scottericpetersen/CAFFEINE/paper/logs/group_test/endpoint_log_pod3_grp.csv

system_time | remote_timestamp | latency_ms | sequence_number
2025-05-15T11:13:07.513176 | 1747321987.007723 | 505.432 | 0
2025-05-15T11:13:07.515925 | 1747321987.017425 | 498.486 | 1
2025-05-15T11:13:07.518675 | 1747321987.027419 | 491.247 | 2
2025-05-15T11:13:07.521302 | 1747321987.397427 | 123.865 | 39
2025-05-15T11:13:07.523168 | 1747321987.407426 | 115.732 | 40
2025-05-15T11:13:07.523786 | 1747321987.417427 | 106.354 | 41
2025-05-15T11:13:07.525354 | 1747321987.427426 | 97.92 | 42
2025-05-15T11:13:07.526999 | 1747321987.437427 | 89.564 | 43
2025-05-15T11:13:07.528279 | 1747321987.457427 | 70.845 | 45
2025-05-15T11:13:07.528917 | 1747321987.447426 | 81.481 | 44
2025-05-15T11:13:07.532104 | 1747321987.467426 | 64.671 | 46
2025-05-15T11:13:07.532553 | 1747321987.477427 | 55.121 | 47
2025-05-15T11:13:07.534322 | 1747321987.487427 | 46.89 | 48
2025-05-15T11:13:07.536326 | 1747321987.497427 | 38.891 | 49
2025-05-15T11:13:07.536886 | 1747321987.507427 | 29.455 | 50
2025-05-15T11:13:07.537390 | 1747321987.517427 | 19.956 | 51
2025-05-15T11:13:07.544280 | 1747321987.527427 | 16.845 | 52
2025-05-15T11:13:07.554681 | 1747321987.537427 | 17.248 | 53
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
