scottericpetersen/CAFFEINE/paper/logs/single_tests/endpoint_log_pod1.csv

system_time | remote_timestamp | latency_ms | sequence_number
2025-05-15T10:38:45.889145 | 1747319924.829069 | 1060.061 | 0
2025-05-15T10:38:45.890400 | 1747319925.834085 | 56.305 | 1
2025-05-15T10:38:45.891751 | 1747319925.843692 | 48.051 | 2
2025-05-15T10:38:45.970882 | 1747319925.863703 | 107.163 | 4
2025-05-15T10:38:45.971901 | 1747319925.873694 | 98.206 | 5
2025-05-15T10:38:45.975954 | 1747319925.913693 | 62.253 | 9
2025-05-15T10:38:45.971991 | 1747319925.883692 | 88.297 | 6
2025-05-15T10:38:45.971718 | 1747319925.893693 | 77.856 | 7
2025-05-15T10:38:45.974419 | 1747319925.903691 | 70.715 | 8
2025-05-15T10:38:45.979967 | 1747319925.933692 | 46.263 | 11
2025-05-15T10:38:45.980275 | 1747319925.923693 | 56.58 | 10
2025-05-15T10:38:46.019493 | 1747319925.943693 | 75.794 | 12
2025-05-15T10:38:46.019986 | 1747319925.953692 | 66.29 | 13
2025-05-15T10:38:46.090310 | 1747319925.963691 | 126.611 | 14
2025-05-15T10:38:46.093204 | 1747319925.973693 | 119.503 | 15
2025-05-15T10:38:46.094900 | 1747319925.983693 | 111.199 | 16
2025-05-15T10:38:46.097762 | 1747319925.993692 | 104.064 | 17
2025-05-15T10:38:46.098465 | 1747319926.003692 | 94.765 | 18
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
