scottericpetersen/CAFFEINE/paper/logs/single_tests/endpoint_log_pod2.csv

system_time | remote_timestamp | latency_ms | sequence_number
2025-05-15T10:51:22.721829 | 1747320682.204614 | 517.201 | 0
2025-05-15T10:51:22.724334 | 1747320682.214574 | 509.746 | 1
2025-05-15T10:51:22.732373 | 1747320682.614575 | 117.79 | 41
2025-05-15T10:51:22.733591 | 1747320682.224572 | 509.002 | 2
2025-05-15T10:51:22.734574 | 1747320682.604577 | 129.982 | 40
2025-05-15T10:51:22.734827 | 1747320682.624576 | 110.248 | 42
2025-05-15T10:51:22.736163 | 1747320682.634575 | 101.577 | 43
2025-05-15T10:51:22.742255 | 1747320682.654575 | 87.672 | 45
2025-05-15T10:51:22.742499 | 1747320682.664576 | 77.92 | 46
2025-05-15T10:51:22.743621 | 1747320682.644577 | 99.038 | 44
2025-05-15T10:51:22.745315 | 1747320682.674575 | 70.732 | 47
2025-05-15T10:51:22.748814 | 1747320682.684576 | 64.229 | 48
2025-05-15T10:51:22.749644 | 1747320682.694575 | 55.063 | 49
2025-05-15T10:51:22.750121 | 1747320682.704576 | 45.54 | 50
2025-05-15T10:51:22.750343 | 1747320682.714575 | 35.758 | 51
2025-05-15T10:51:22.751264 | 1747320682.724576 | 26.685 | 52
2025-05-15T10:51:22.752816 | 1747320682.734574 | 18.235 | 53
2025-05-15T10:51:22.762646 | 1747320682.744576 | 18.063 | 54
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
