scottericpetersen/CAFFEINE/paper/logs/single_tests/plots/all_pods_overlay.png

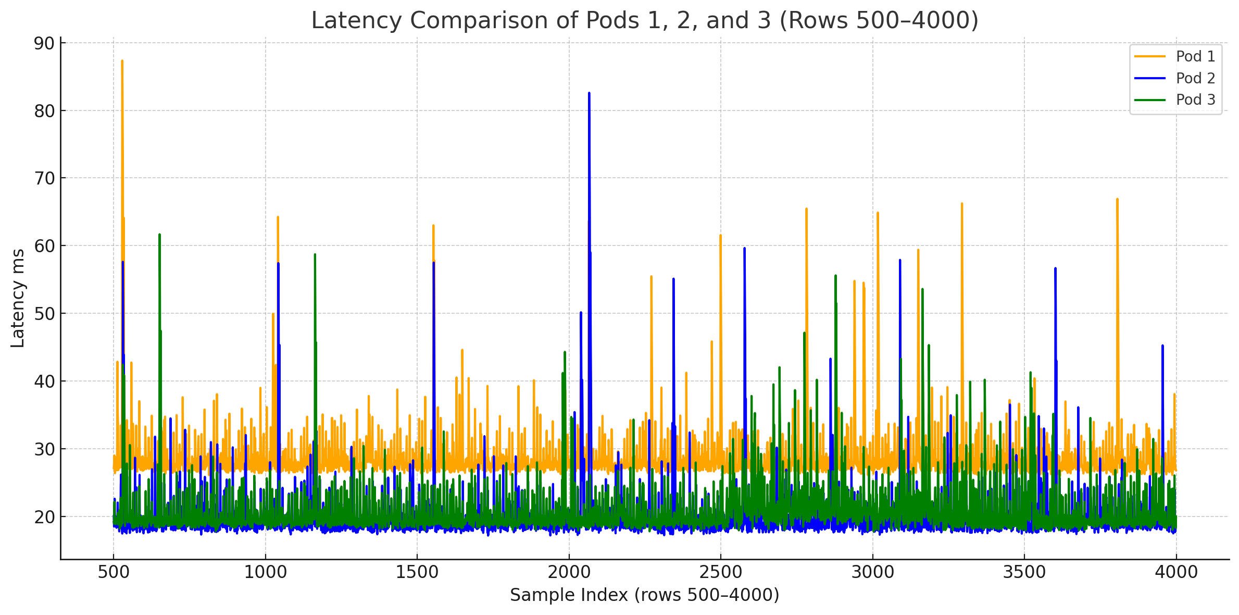
paper/logs/single_tests/plots/all_pods_overlay.png
