scottericpetersen/CAFFEINE/paper/logs/single_tests/plots/pod1_latency.png

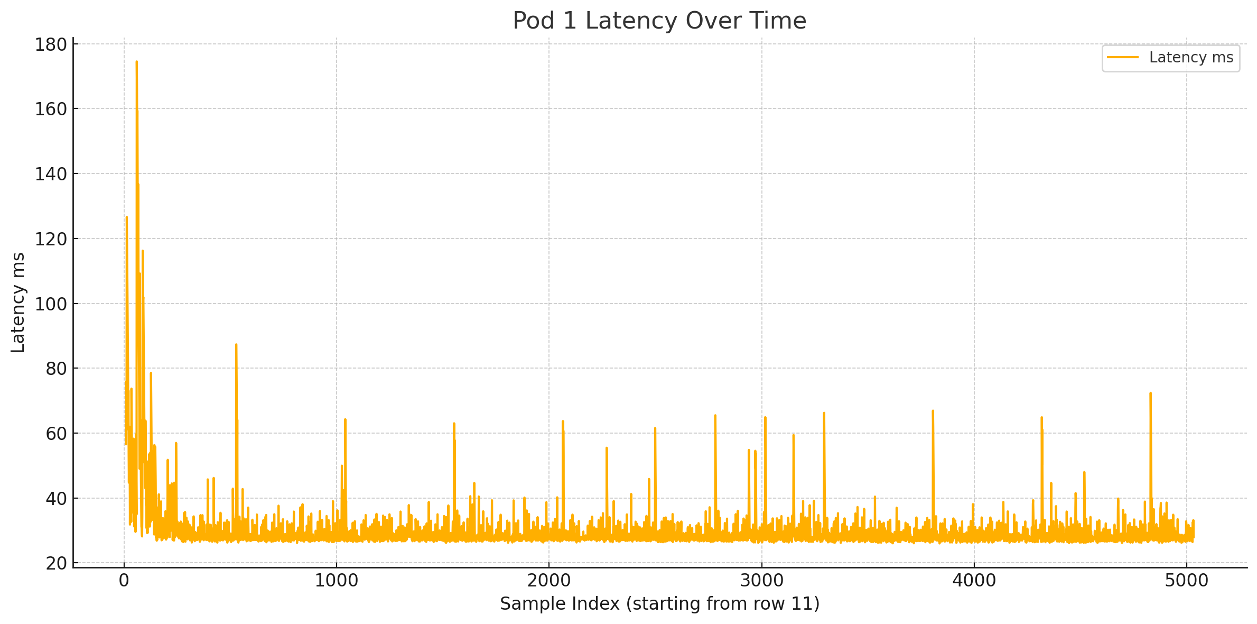
paper/logs/single_tests/plots/pod1_latency.png
