scottericpetersen/CAFFEINE/paper/logs/single_tests/plots/pod2_latency.png

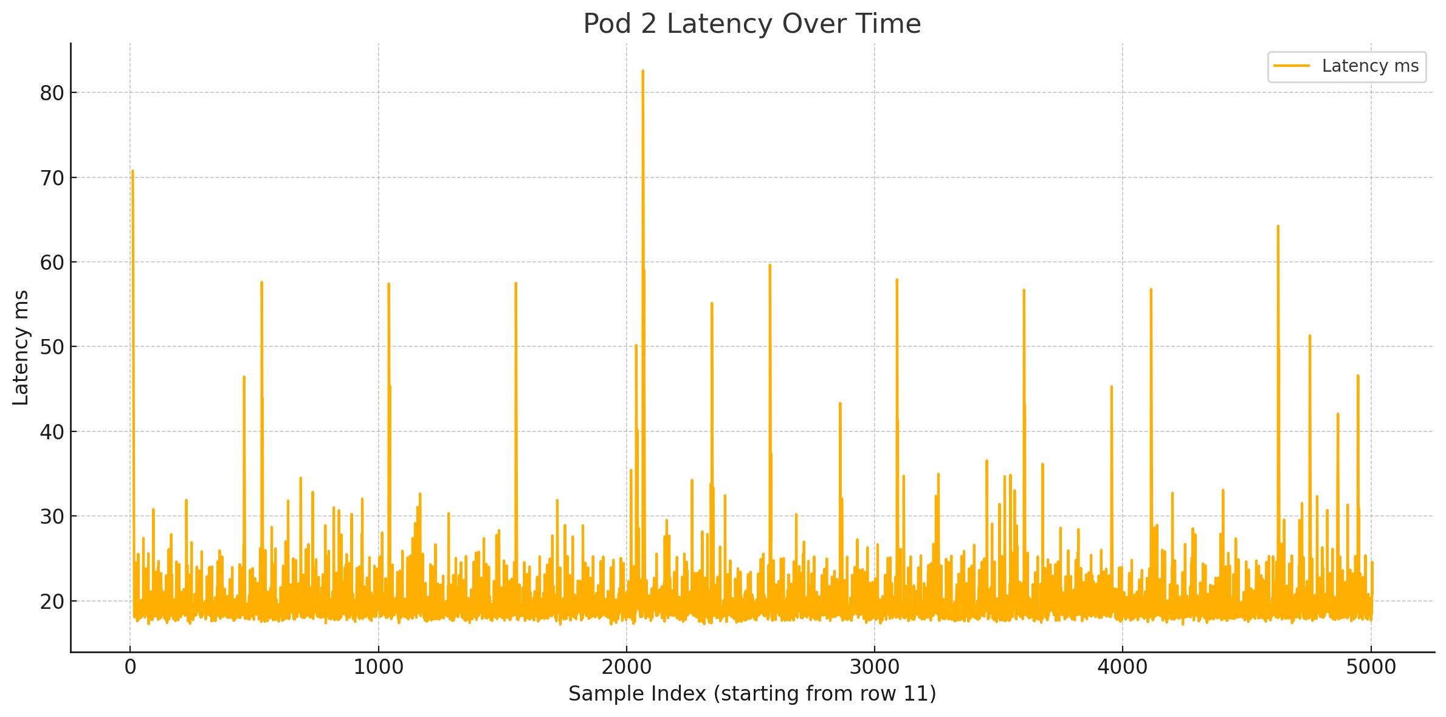
paper/logs/single_tests/plots/pod2_latency.png
