scottericpetersen/CAFFEINE/paper/logs/single_tests/plots/pod3_latency.png

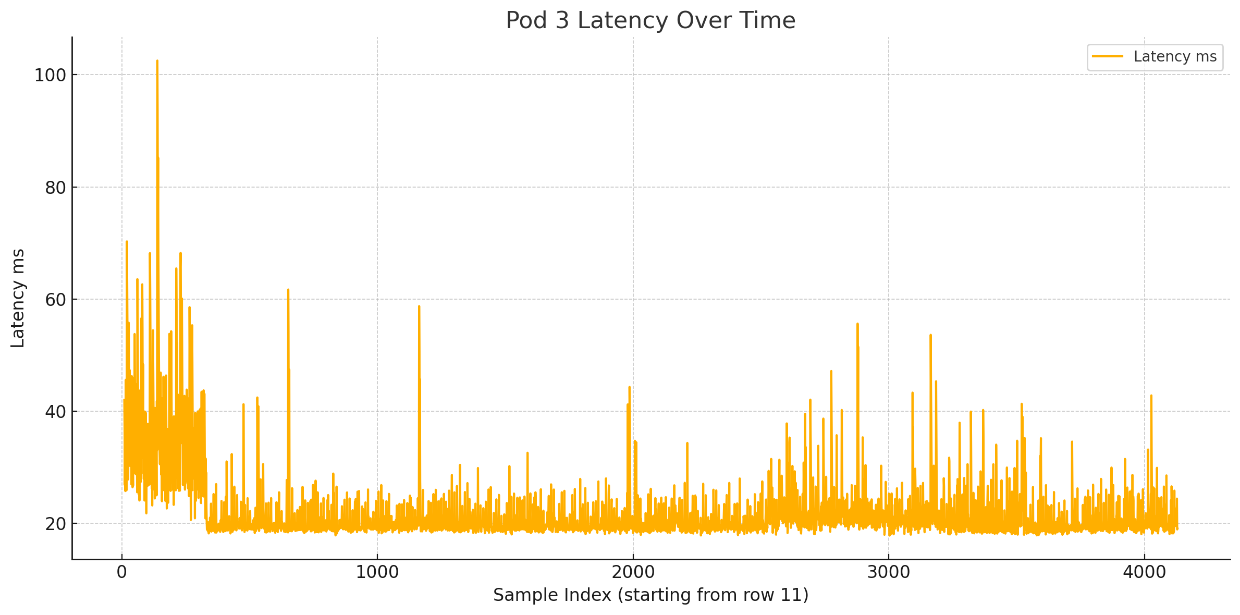
paper/logs/single_tests/plots/pod3_latency.png
